Def12345678/smol-FC-G474-REV-A/smol-FC-G474-REV-A/footprints&symbols/B3U-1000P/KEY-SMD_2P-L3.0-W2.5-H1.6-LS4.0.step

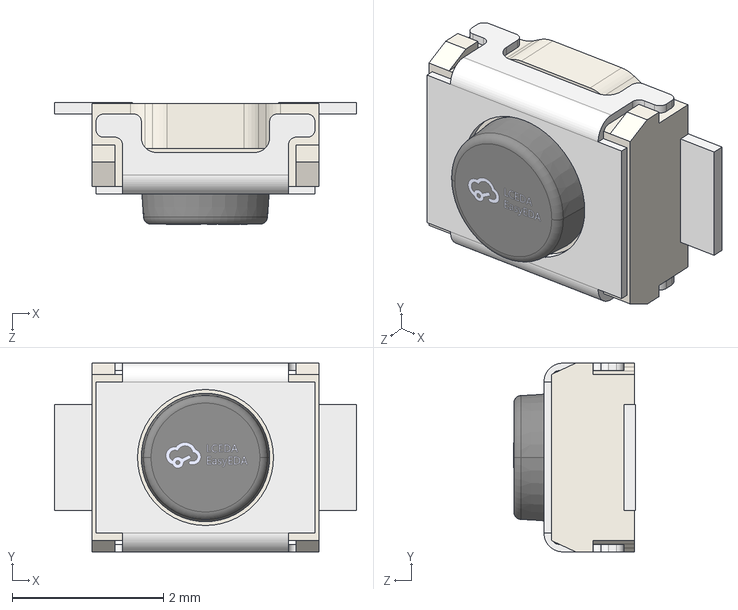
[picture p17: CAD file, 2026-06-24]
smol-FC-G474-REV-A/footprints&symbols/B3U-1000P/KEY-SMD_2P-L3.0-W2.5-H1.6-LS4.0.step
4.00 x 2.50 x 1.61 mm
