Def12345678/smol-FC-G474-REV-A/smol-FC-G474-REV-A/footprints&symbols/inductor/XAL4030-682MEC--3DModel-STEP-56544.STEP

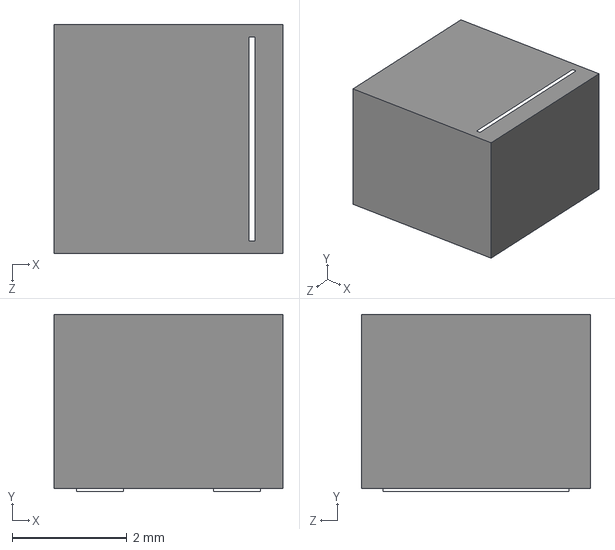
[picture p18: CAD file, 2026-06-24]
smol-FC-G474-REV-A/footprints&symbols/inductor/XAL4030-682MEC--3DModel-STEP-56544.STEP
4.00 x 3.10 x 4.00 mm
